heig-vd-ihm2017/party-device/code/src/Modes.h

#ifndef MODES_H
#define MODES_H

#include "modes/FixedRateRythmGame.h"
#include "modes/SoundLevel.h"
#include "modes/ColorSoundLevel.h"
#include "modes/MovingPoint.h"
#include "modes/LineSoundLevel.h"
#include "modes/CascadeSoundLevel.h"
#include "modes/OneRandomLedRainbow.h"
#include "modes/SideBySide.h"

#endif // MODES_H
